SmartMaatt/Washing-machine-detector-ESP32/Software/Source/sample.h

//Minecraft level up sound ;D
const unsigned char sample_flac[] PROGMEM = {
  0x66, 0x4C, 0x61, 0x43, 0x00, 0x00, 0x00, 0x22, 0x10, 0x00, 0x10, 0x00,
  0x00, 0x0C, 0xFD, 0x00, 0x1C, 0x85, 0x0A, 0xC4, 0x42, 0xF0, 0x00, 0x00,
  0xA8, 0xEF, 0x17, 0x5F, 0x1F, 0xA3, 0x91, 0x8D, 0x12, 0xCE, 0x82, 0x23,
  0x01, 0xA1, 0x97, 0xC2, 0x68, 0x01, 0x84, 0x00, 0x00, 0xA9, 0x20, 0x00,
  0x00, 0x00, 0x72, 0x65, 0x66, 0x65, 0x72, 0x65, 0x6E, 0x63, 0x65, 0x20,
  0x6C, 0x69, 0x62, 0x46, 0x4C, 0x41, 0x43, 0x20, 0x31, 0x2E, 0x33, 0x2E,
  0x31, 0x20, 0x32, 0x30, 0x31, 0x34, 0x31, 0x31, 0x32, 0x35, 0x05, 0x00,
  0x00, 0x00, 0x16, 0x00, 0x00, 0x00, 0x53, 0x6F, 0x66, 0x74, 0x77, 0x61,
  0x72, 0x65, 0x3D, 0x4C, 0x61, 0x76, 0x66, 0x35, 0x38, 0x2E, 0x32, 0x39,
  0x2E, 0x31, 0x30, 0x30, 0x10, 0x00, 0x00, 0x00, 0x6D, 0x61, 0x6A, 0x6F,
  0x72, 0x5F, 0x62, 0x72, 0x61, 0x6E, 0x64, 0x3D, 0x64, 0x61, 0x73, 0x68,
  0x0F, 0x00, 0x00, 0x00, 0x6D, 0x69, 0x6E, 0x6F, 0x72, 0x5F, 0x76, 0x65,
  0x72, 0x73, 0x69, 0x6F, 0x6E, 0x3D, 0x30, 0x1A, 0x00, 0x00, 0x00, 0x63,
  0x6F, 0x6D, 0x70, 0x61, 0x74, 0x69, 0x62, 0x6C, 0x65, 0x5F, 0x62, 0x72,
  0x61, 0x6E, 0x64, 0x73, 0x3D, 0x69, 0x73, 0x6F, 0x36, 0x6D, 0x70, 0x34,
  0x31, 0x1E, 0x00, 0x00, 0x00, 0x54, 0x49, 0x54, 0x4C, 0x45, 0x3D, 0x6D,
  0x69, 0x6E, 0x65, 0x63, 0x72, 0x61, 0x66, 0x74, 0x20, 0x6C, 0x65, 0x76,
  0x65, 0x6C, 0x20, 0x75, 0x70, 0x20, 0x73, 0x6F, 0x75, 0x6E, 0x64, 0xFF,
  0xF8, 0xC9, 0xA8, 0x00, 0x8D, 0x12, 0xFF, 0xFF, 0x0C, 0x93, 0xE9, 0x24,
  0x92, 0x49, 0x2A, 0x38, 0x87, 0x25, 0xBA, 0x4B, 0xA5, 0x45, 0x49, 0xC8,
  0x53, 0x14, 0x9F, 0x65, 0x23, 0xB7, 0xD5, 0x3E, 0x95, 0x15, 0xBA, 0x74,
  0xF1, 0x3A, 0x74, 0x53, 0x1C, 0x9F, 0x49, 0x2A, 0x29, 0x17, 0x4C, 0xA6,
  0x39, 0x97, 0x49, 0x2A, 0x74, 0x54, 0xA9, 0xE6, 0xA9, 0xF5, 0x63, 0x8C,
  0x72, 0x5E, 0xCA, 0xD6, 0xA2, 0x91, 0x74, 0x95, 0x3E, 0x95, 0x14, 0x85,
  0x10, 0x51, 0x1D, 0x25, 0x45, 0x21, 0x49, 0x79, 0x1D, 0xBC, 0x45, 0x6F,
  0x34, 0x95, 0x14, 0x85, 0x27, 0xD5, 0x8A, 0x4F, 0xA4, 0xED, 0xD3, 0xEA,
  0x9D, 0x2D, 0x4E, 0x8A, 0xDD, 0x3A, 0x2B, 0x5E, 0xDE, 0x31, 0x44, 0x39,
  0x9C, 0x8E, 0xDD, 0x3C, 0x4F, 0xA7, 0x6E, 0x8A, 0xDF, 0x4B, 0xA5, 0xD2,
  0x5D, 0x53, 0xE9, 0x53, 0xE9, 0x74, 0xBA, 0xA2, 0xB5, 0xA8, 0xAD, 0xD1,
  0x48, 0x53, 0x3B, 0x5A, 0x8A, 0x45, 0xD9, 0xC4, 0x39, 0xBF, 0x6F, 0xA4,
  0xA8, 0xA6, 0x14, 0x63, 0x99, 0xDB, 0xA7, 0xD5, 0x9D, 0x95, 0xBA, 0x2B,
  0x7D, 0x94, 0xC2, 0x88, 0xED, 0x67, 0x21, 0x4C, 0xED, 0x6E, 0x97, 0x5D,
  0x51, 0x5B, 0xA2, 0x91, 0xC8, 0xED, 0x6A, 0x38, 0x82, 0x84, 0x1C, 0x62,
  0xB7, 0x8C, 0x53, 0x2C, 0x45, 0x6B, 0x74, 0xBA, 0xEC, 0xA4, 0x29, 0x97,
  0x5D, 0x53, 0xEC, 0xAC, 0xAD, 0x7B, 0x7D, 0x2E, 0x92, 0xE9, 0x75, 0xD2,
  0x5D, 0x39, 0x0A, 0x65, 0x88, 0xA4, 0x76, 0xFA, 0xA5, 0x92, 0x54, 0xFA,
  0x4A, 0x8A, 0x47, 0x21, 0x44, 0x14, 0x62, 0xE6, 0x29, 0x9D, 0x95, 0xBE,
  0x95, 0x3E, 0x95, 0x14, 0x8E, 0xDD, 0x3A, 0x78, 0x8A, 0x47, 0x6F, 0xA5,
  0x4F, 0xAA, 0x79, 0xA5, 0x45, 0x42, 0xCA, 0xDE, 0x27, 0x88, 0xAD, 0x6A,
  0x2A, 0x4A, 0x8A, 0xDF, 0x49, 0x74, 0xBA, 0x54, 0xB7, 0x49, 0x95, 0x95,
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
};
